Erik84750/Nextion_DCC-EX_enclosure/Nextion_3-2_inch_RPi_Pico_v2_text-lid.stl

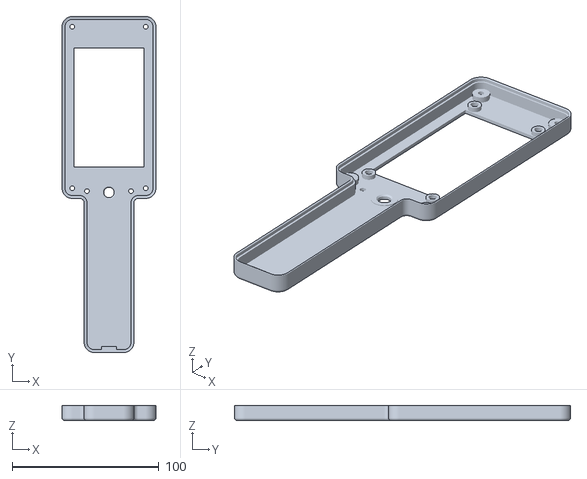
[picture p15: CAD file, 2024-11-09]
Nextion_3-2_inch_RPi_Pico_v2_text-lid.stl
64.0 x 229.0 x 10.5
