Erik84750/Nextion_DCC-EX_enclosure/Nextion_4-3_inch_RPi_Pico_2-batt_v2_text-lid.stl

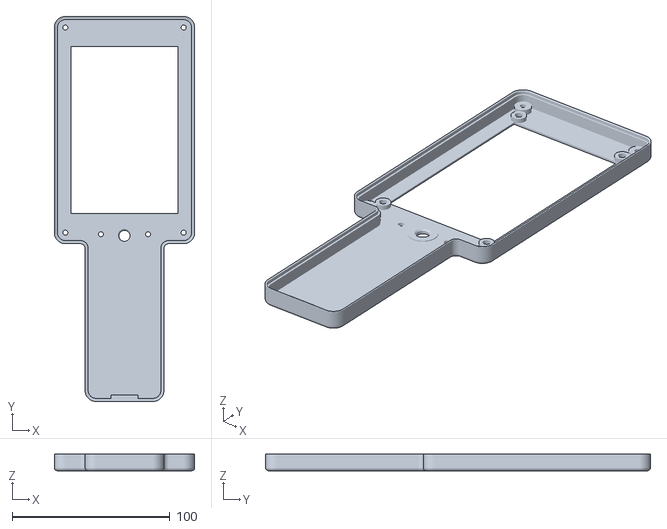
[picture p16: CAD file, 2024-11-09]
Nextion_4-3_inch_RPi_Pico_2-batt_v2_text-lid.stl
89.0 x 244.0 x 10.5
