Erik84750/Nextion_DCC-EX_enclosure/Nextion_4-3_inch_RPi_Pico_2-batt_v2_text-bottom.stl

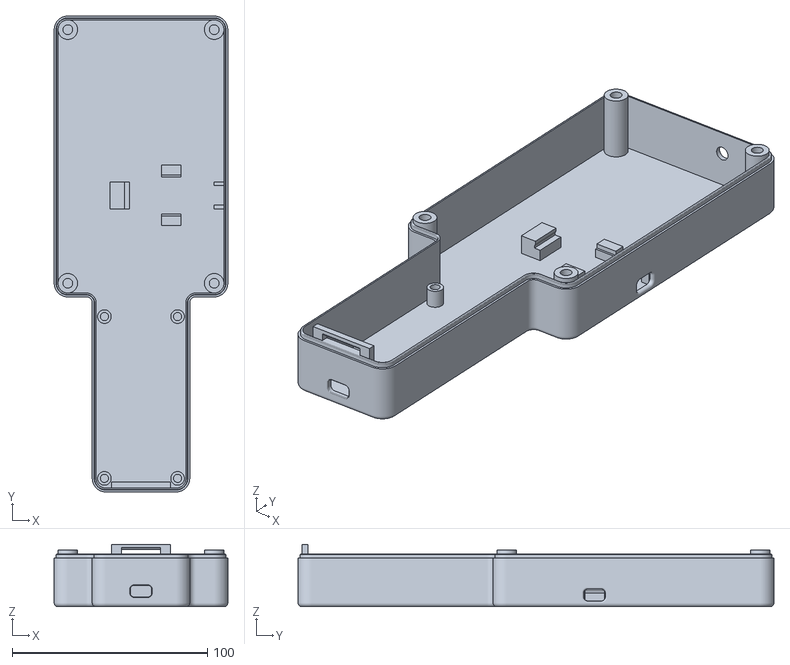
[picture p17: CAD file, 2024-11-09]
Nextion_4-3_inch_RPi_Pico_2-batt_v2_text-bottom.stl
89.0 x 244.0 x 32.0
