Erik84750/Nextion_DCC-EX_enclosure/Nextion_3-5_inch_enclosure_text-bottom.stl

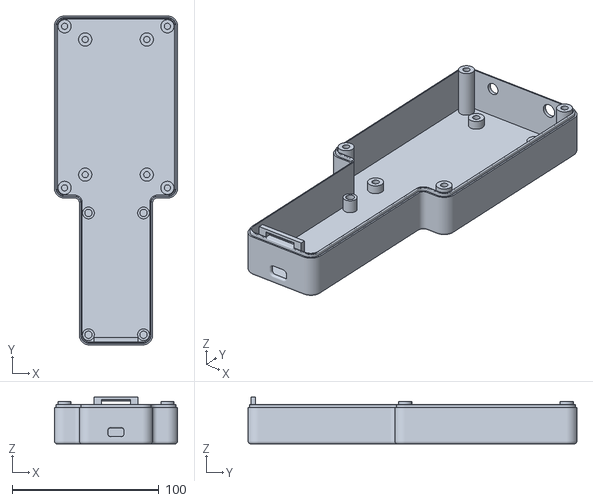
[picture p19: CAD file, 2024-11-09]
Nextion_3-5_inch_enclosure_text-bottom.stl
84.0 x 224.0 x 32.0
