Erik84750/Nextion_DCC-EX_enclosure/Nextion_3-2_inch_enclosure_text-lid.stl

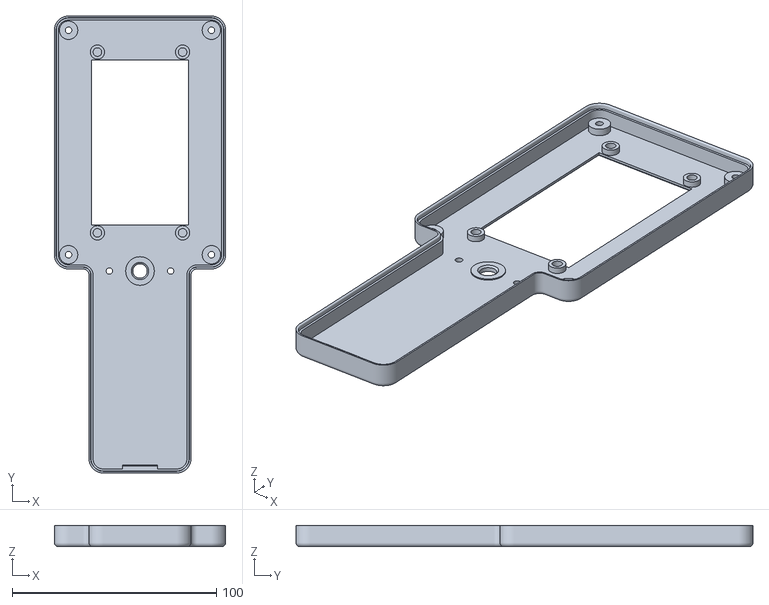
[picture p21: CAD file, 2024-11-09]
Nextion_3-2_inch_enclosure_text-lid.stl
84.0 x 224.0 x 10.5
